patrickjahns/esp_rgbww_controller/pictures/eagle_complete.png

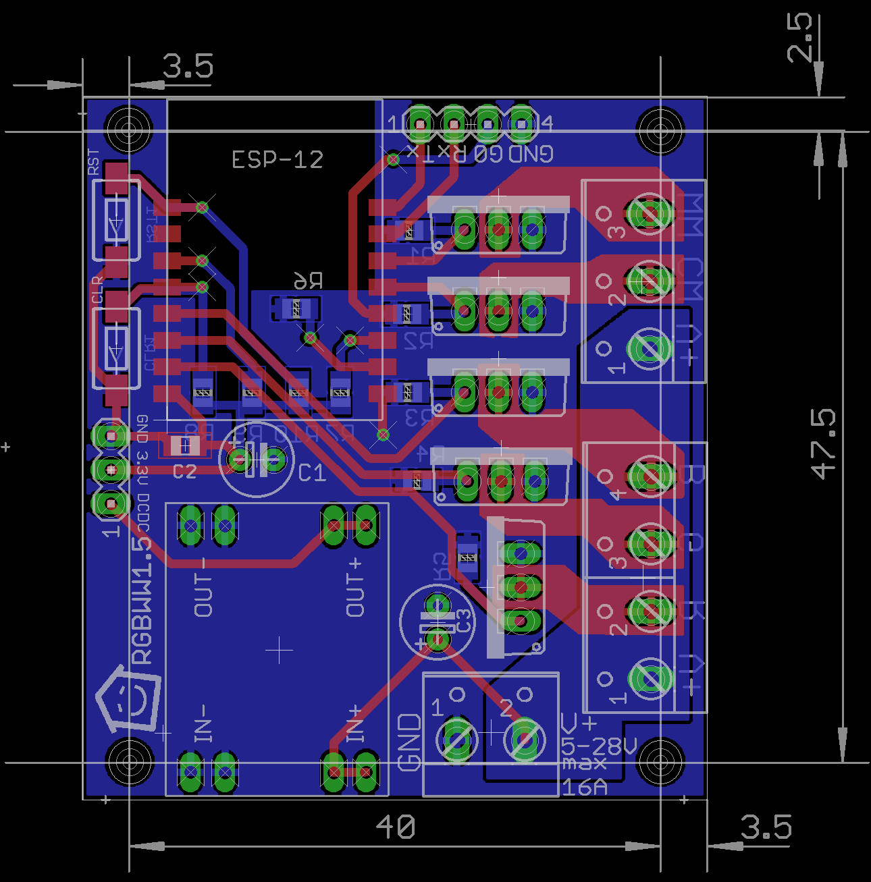
pictures/eagle_complete.png
