patrickjahns/esp_rgbww_controller/pictures/eagle_top.png

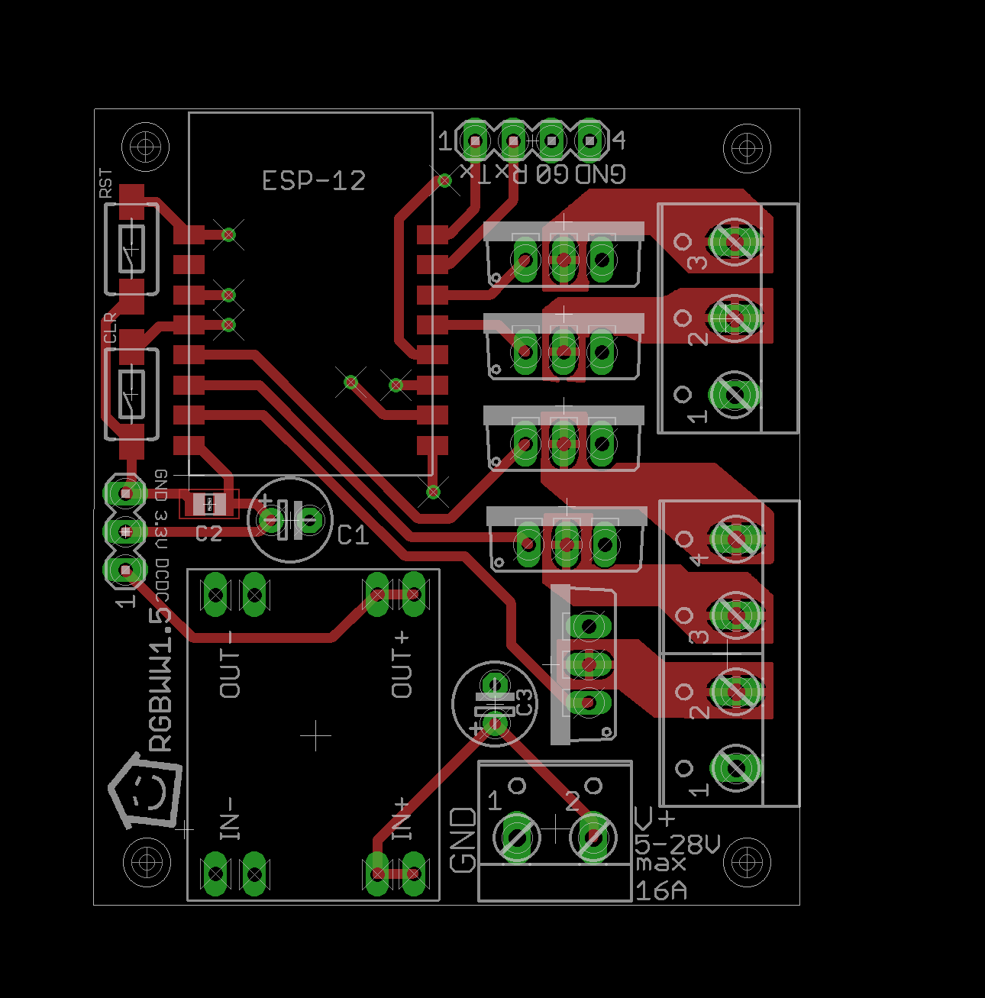
pictures/eagle_top.png
